msekatchev/IWCDCameraHousing/solidworks parts and assembly/PVC Parts/8in PVC Flange Closed - Dome Hole.SLDPRT

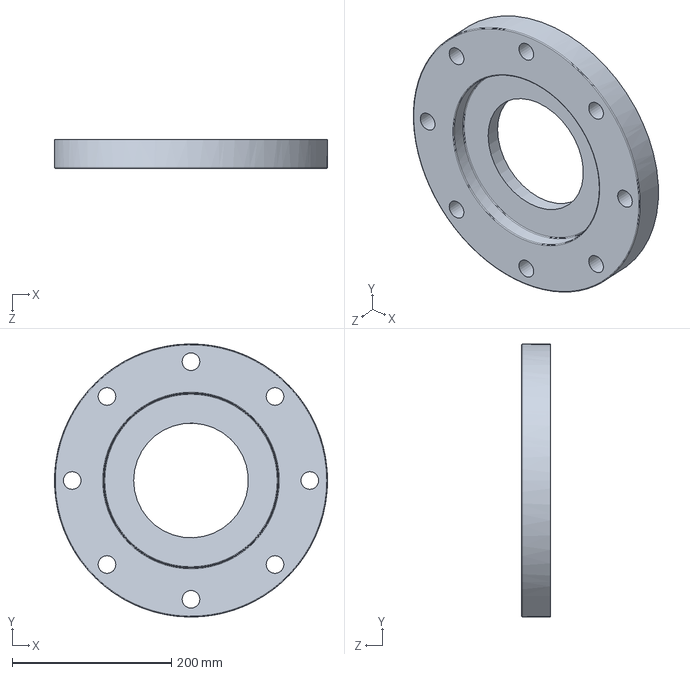
[picture p16: CAD file, 2021-06-16]
solidworks parts and assembly/PVC Parts/8in PVC Flange Closed - Dome Hole.SLDPRT
342.9 x 342.8 x 36.5 mm
