msekatchev/IWCDCameraHousing/solidworks parts and assembly/piston-FrontRing.SLDPRT

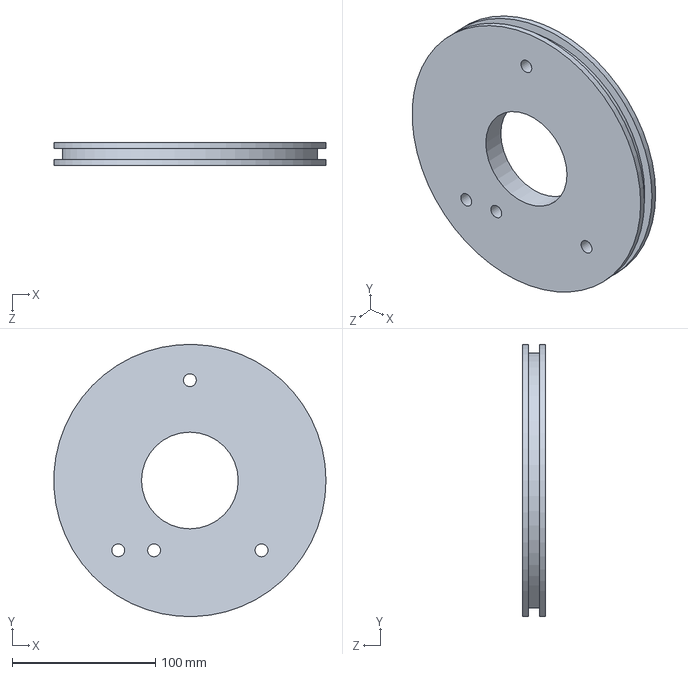
[picture p17: CAD file, 2021-06-16]
solidworks parts and assembly/piston-FrontRing.SLDPRT
189.8 x 189.9 x 16.0 mm
