msekatchev/IWCDCameraHousing/solidworks parts and assembly/PVC Parts/8in PVC Cap.SLDPRT

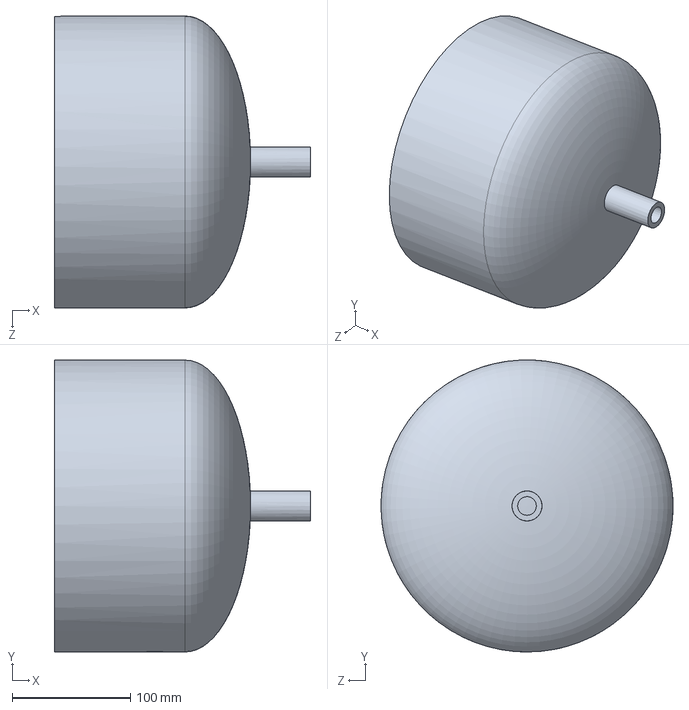
[picture p18: CAD file, 2021-04-09]
solidworks parts and assembly/PVC Parts/8in PVC Cap.SLDPRT
216.9 x 247.1 x 247.1 mm
