msekatchev/IWCDCameraHousing/metalHousingDesign/6 INCH Rayotek Dome.SLDPRT

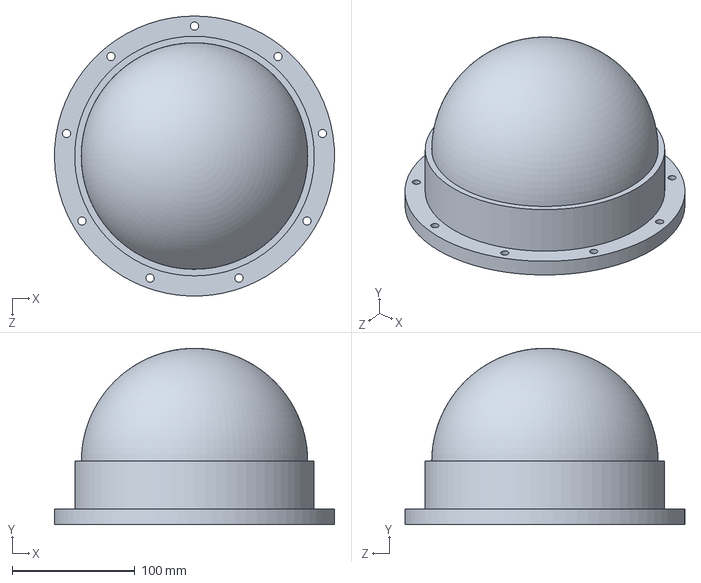
[picture p19: CAD file, 2022-03-02]
metalHousingDesign/6 INCH Rayotek Dome.SLDPRT
228.5 x 144.0 x 228.5 mm
