msekatchev/IWCDCameraHousing/solidworks parts and assembly/PVC Parts/6in PVC Pipe.SLDPRT

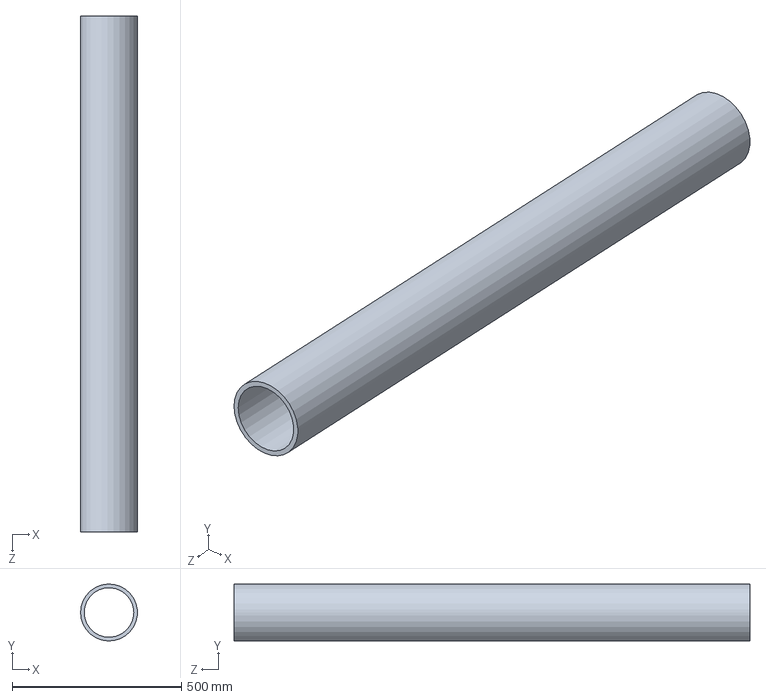
[picture p20: CAD file, 2021-04-09]
solidworks parts and assembly/PVC Parts/6in PVC Pipe.SLDPRT
168.3 x 168.0 x 1524.0 mm
