msekatchev/IWCDCameraHousing/metalHousingDesign/XDE2534-long.SLDPRT

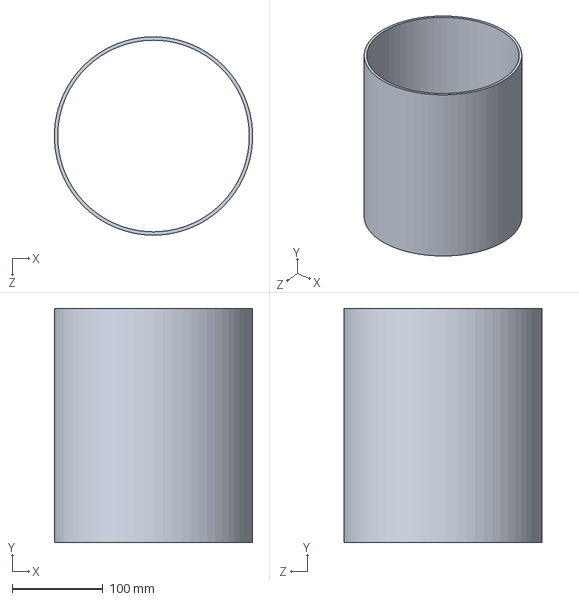
[picture p21: CAD file, 2022-01-20]
metalHousingDesign/XDE2534-long.SLDPRT
218.8 x 258.4 x 219.1 mm
