msekatchev/IWCDCameraHousing/metalHousingDesign/XDE2535.SLDPRT

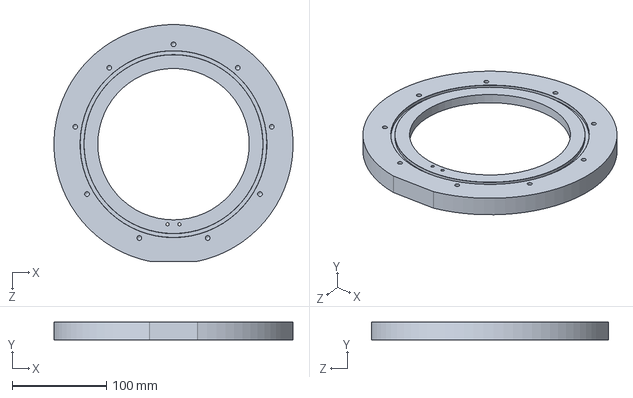
[picture p22: CAD file, 2022-01-20]
metalHousingDesign/XDE2535.SLDPRT
253.8 x 19.1 x 251.3 mm
