msekatchev/IWCDCameraHousing/solidworks parts and assembly/piston-SpacerTube.SLDPRT

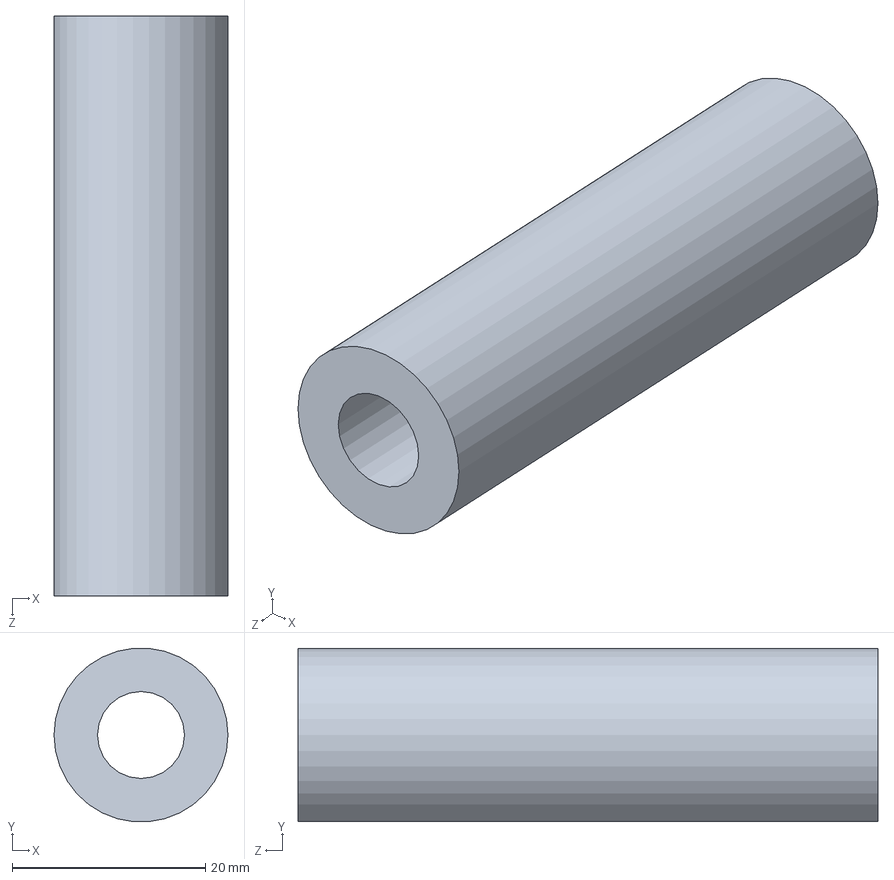
[picture p23: CAD file, 2021-04-09]
solidworks parts and assembly/piston-SpacerTube.SLDPRT
18.0 x 17.9 x 60.0 mm
