msekatchev/IWCDCameraHousing/solidworks parts and assembly/PVC Parts/8in PVC Flange Closed.SLDPRT

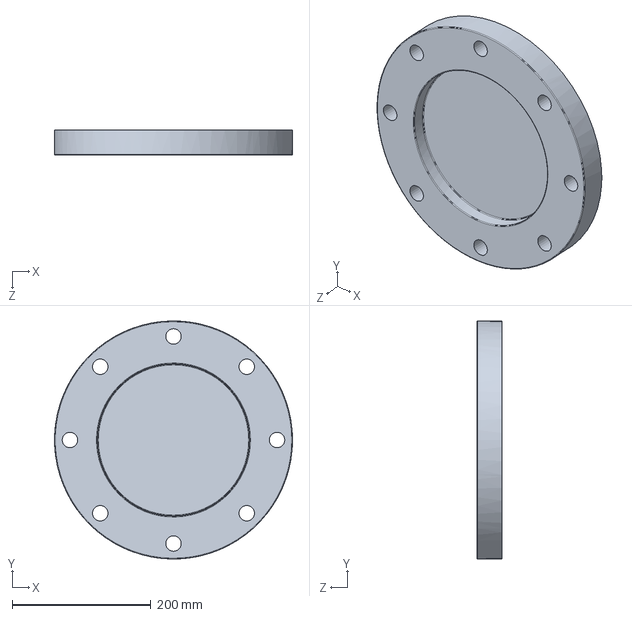
[picture p24: CAD file, 2021-04-09]
solidworks parts and assembly/PVC Parts/8in PVC Flange Closed.SLDPRT
342.9 x 342.8 x 36.5 mm
