msekatchev/IWCDCameraHousing/solidworks parts and assembly/PVC Parts/8in Buna-N Gasket.SLDPRT

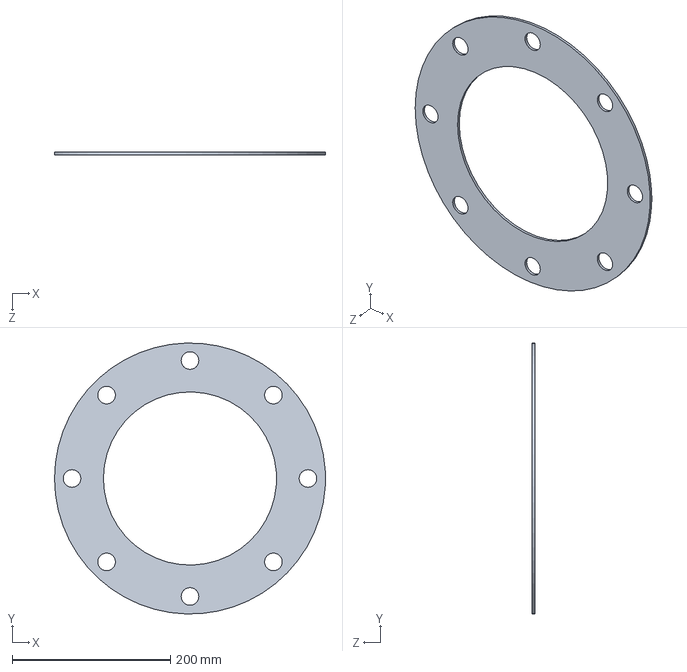
[picture p25: CAD file, 2021-04-09]
solidworks parts and assembly/PVC Parts/8in Buna-N Gasket.SLDPRT
342.9 x 342.7 x 3.17 mm
