msekatchev/IWCDCameraHousing/metalHousingDesign/XDE2540.SLDPRT

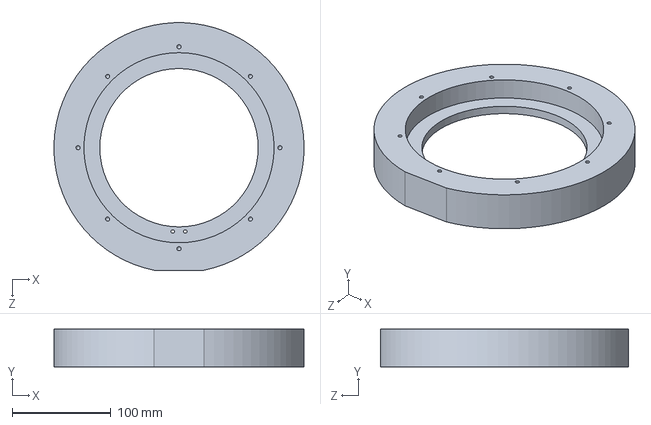
[picture p26: CAD file, 2022-01-20]
metalHousingDesign/XDE2540.SLDPRT
253.8 x 38.1 x 251.3 mm
