msekatchev/IWCDCameraHousing/solidworks parts and assembly/PVC Parts/8in PVC Pipe.SLDPRT

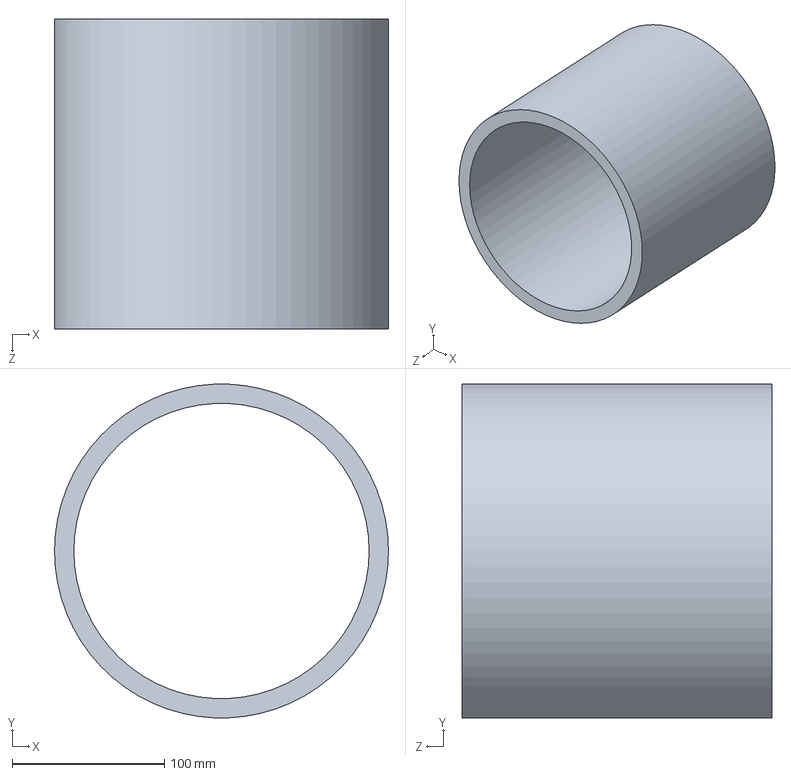
[picture p27: CAD file, 2021-04-09]
solidworks parts and assembly/PVC Parts/8in PVC Pipe.SLDPRT
219.1 x 218.8 x 203.2 mm
