msekatchev/IWCDCameraHousing/solidworks parts and assembly/SPRING.SLDPRT

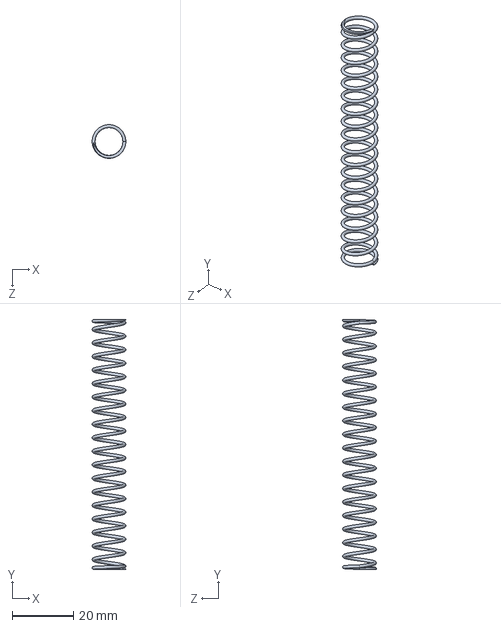
[picture p28: CAD file, 2021-04-09]
solidworks parts and assembly/SPRING.SLDPRT
11.0 x 81.5 x 11.0 mm
