msekatchev/IWCDCameraHousing/metalHousingDesign/XDE2539.SLDPRT

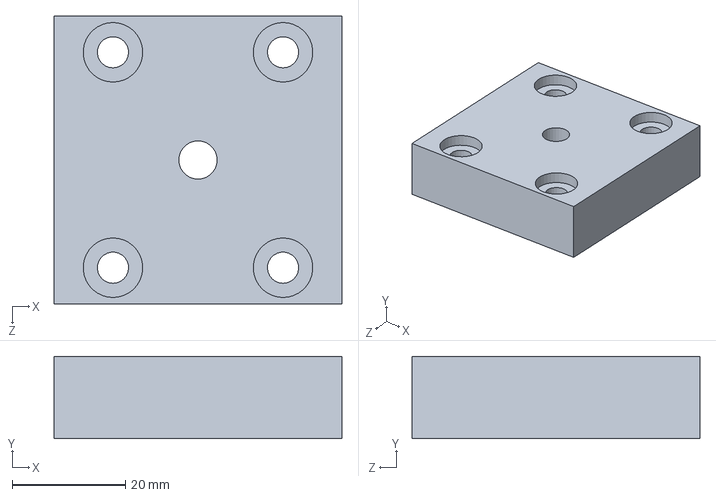
[picture p29: CAD file, 2022-01-20]
metalHousingDesign/XDE2539.SLDPRT
50.8 x 14.5 x 50.8 mm
