msekatchev/IWCDCameraHousing/solidworks parts and assembly/PVC Parts/8in PVC Flange.SLDPRT

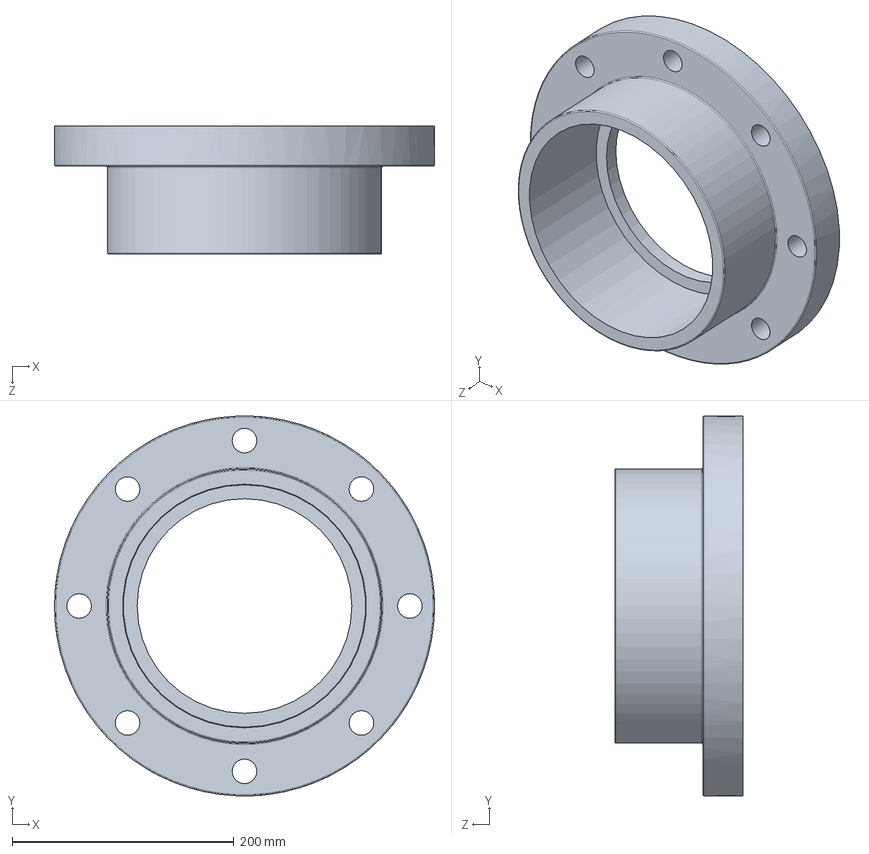
[picture p30: CAD file, 2021-04-09]
solidworks parts and assembly/PVC Parts/8in PVC Flange.SLDPRT
342.9 x 342.7 x 115.9 mm
