msekatchev/IWCDCameraHousing/metalHousingDesign/XDE2536.SLDPRT

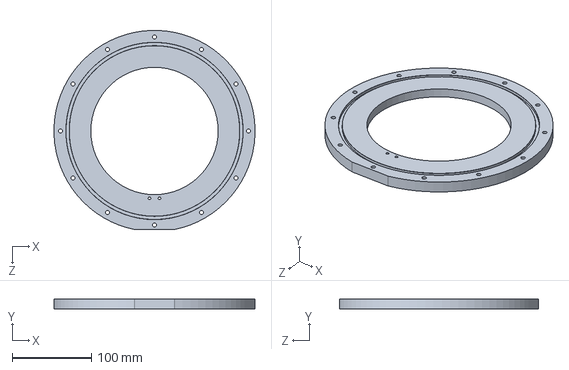
[picture p31: CAD file, 2022-01-20]
metalHousingDesign/XDE2536.SLDPRT
253.8 x 12.7 x 251.3 mm
