msekatchev/IWCDCameraHousing/metalHousingDesign/XDE2534-cut.SLDPRT

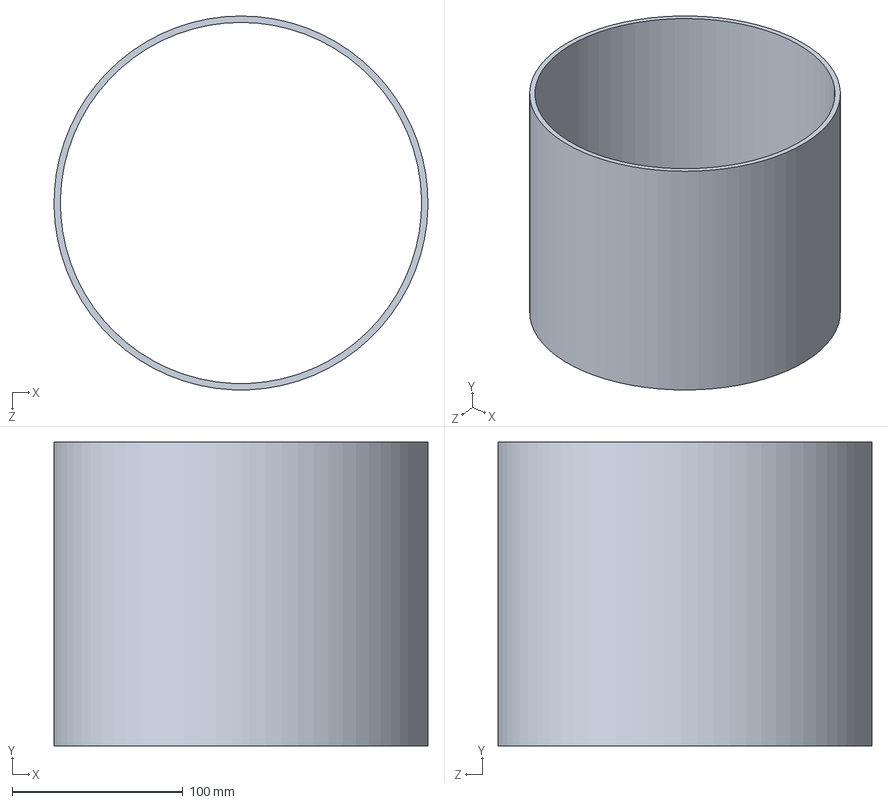
[picture p32: CAD file, 2022-01-20]
metalHousingDesign/XDE2534-cut.SLDPRT
219.0 x 178.0 x 219.1 mm
