msekatchev/IWCDCameraHousing/solidworks parts and assembly/M8 STEEL ROD.SLDPRT

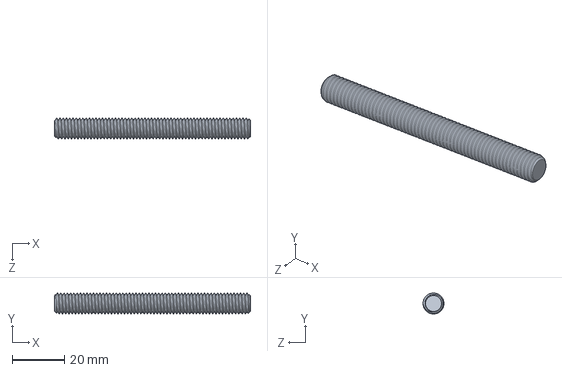
[picture p33: CAD file, 2021-04-09]
solidworks parts and assembly/M8 STEEL ROD.SLDPRT
75.0 x 8.00 x 8.00 mm
