msekatchev/IWCDCameraHousing/metalHousingDesign/XDE2557.SLDPRT

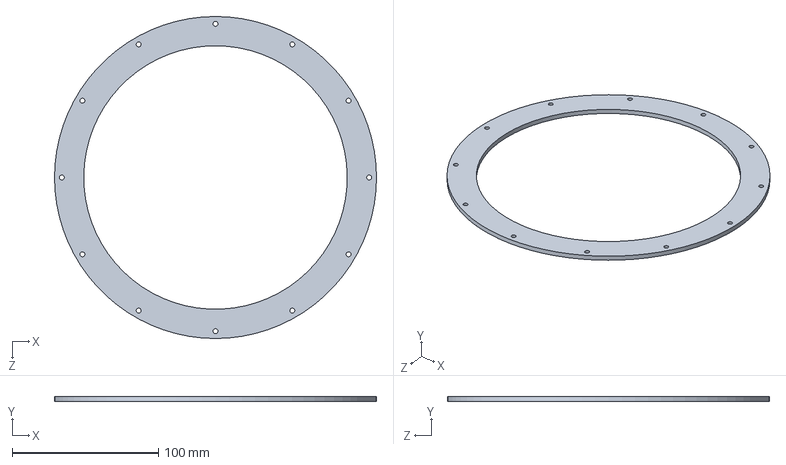
[picture p34: CAD file, 2022-01-20]
metalHousingDesign/XDE2557.SLDPRT
220.0 x 3.17 x 220.0 mm
