msekatchev/IWCDCameraHousing/metalHousingDesign/XDE2538.SLDPRT

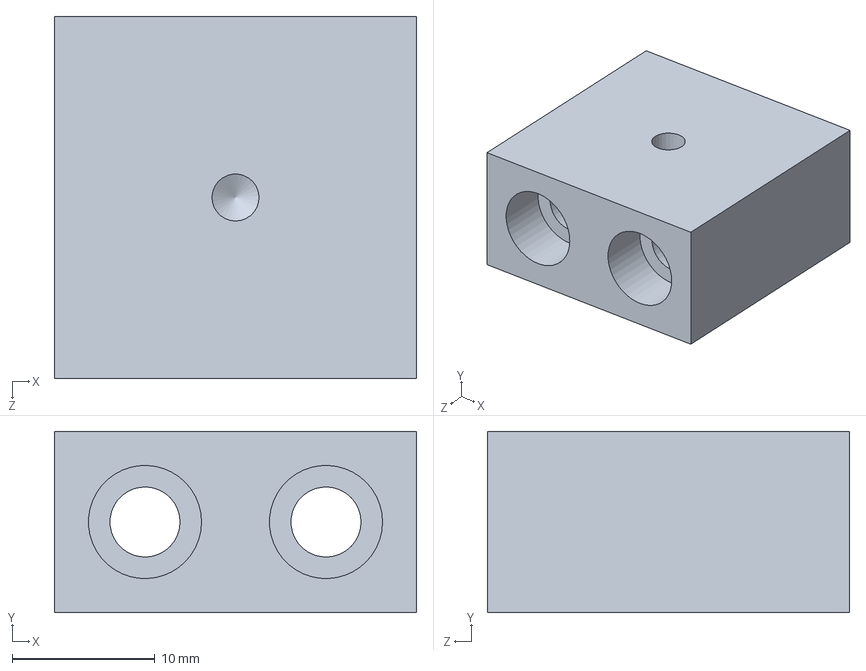
[picture p35: CAD file, 2022-01-20]
metalHousingDesign/XDE2538.SLDPRT
25.4 x 12.7 x 25.4 mm
