msekatchev/IWCDCameraHousing/solidworks parts and assembly/piston-7inO-RING.SLDPRT

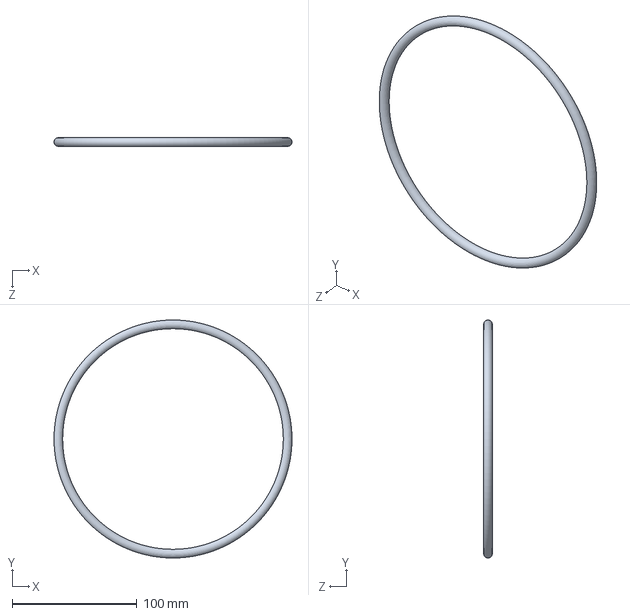
[picture p36: CAD file, 2021-04-09]
solidworks parts and assembly/piston-7inO-RING.SLDPRT
191.1 x 191.1 x 6.98 mm
