msekatchev/IWCDCameraHousing/metalHousingDesign/XDE2532_Nautilus.SLDPRT

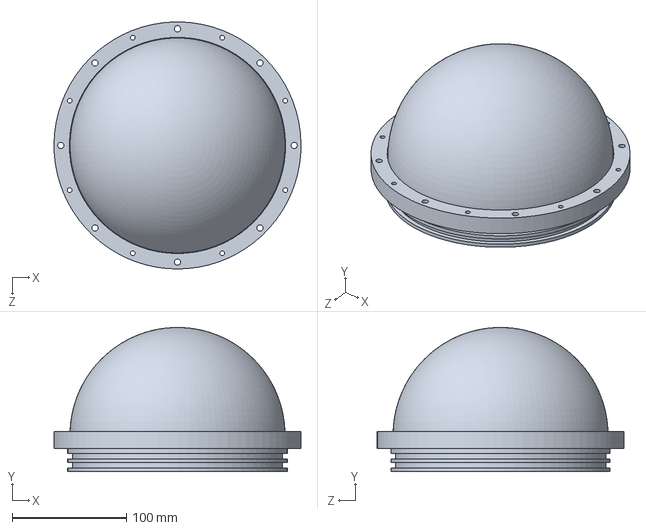
[picture p37: CAD file, 2022-01-20]
metalHousingDesign/XDE2532_Nautilus.SLDPRT
216.0 x 126.0 x 215.9 mm
