msekatchev/IWCDCameraHousing/solidworks parts and assembly/piston-CameraPlate.SLDPRT

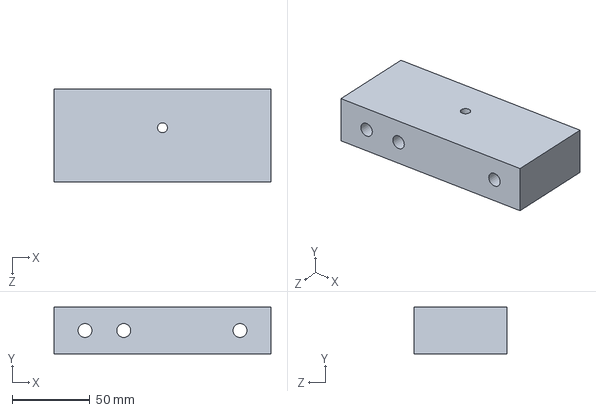
[picture p38: CAD file, 2021-04-09]
solidworks parts and assembly/piston-CameraPlate.SLDPRT
140.0 x 30.0 x 60.0 mm
