msekatchev/IWCDCameraHousing/metalHousingDesign/XDE2556.SLDPRT

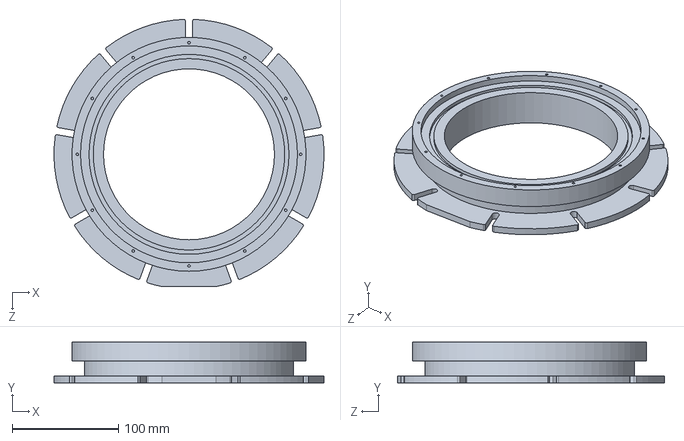
[picture p39: CAD file, 2022-01-20]
metalHousingDesign/XDE2556.SLDPRT
254.0 x 38.1 x 251.3 mm
