msekatchev/IWCDCameraHousing/metalHousingDesign/XDE2532_EZTop.SLDPRT

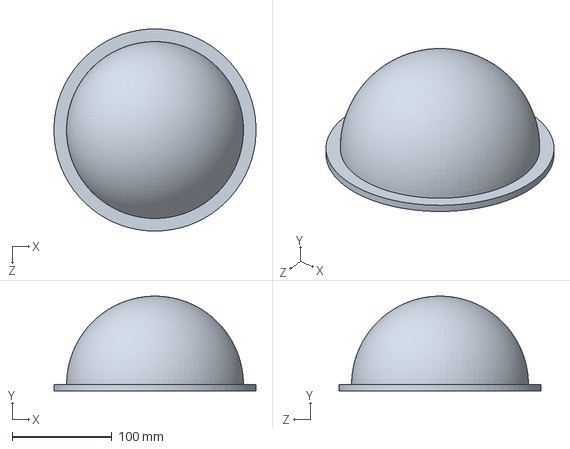
[picture p40: CAD file, 2022-01-20]
metalHousingDesign/XDE2532_EZTop.SLDPRT
203.0 x 95.2 x 203.2 mm
