msekatchev/IWCDCameraHousing/metalHousingDesign/XDE2555.SLDPRT

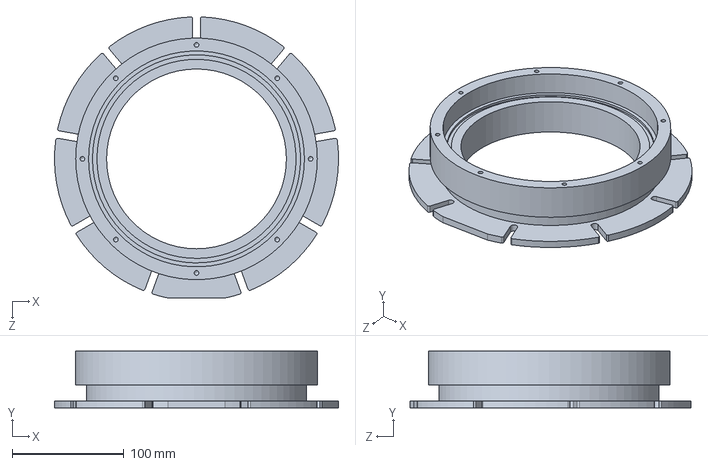
[picture p41: CAD file, 2022-01-20]
metalHousingDesign/XDE2555.SLDPRT
254.0 x 50.8 x 251.3 mm
