msekatchev/IWCDCameraHousing/solidworks parts and assembly/Camera Case-2_V2.SLDPRT

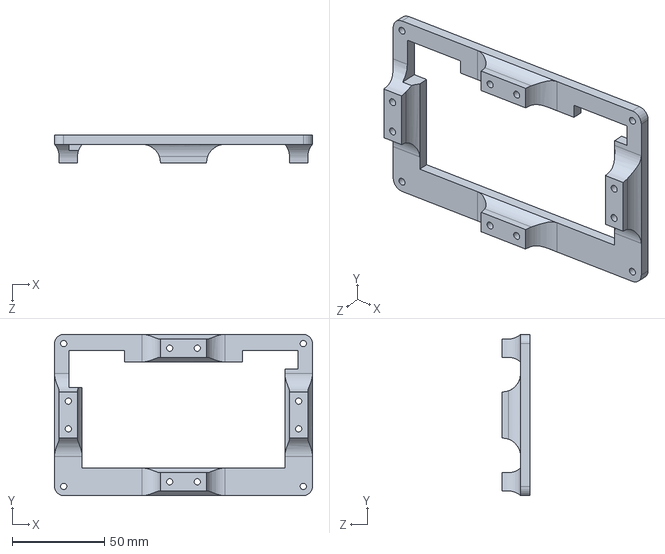
[picture p42: CAD file, 2021-02-12]
solidworks parts and assembly/Camera Case-2_V2.SLDPRT
140.0 x 87.5 x 15.0 mm
