msekatchev/IWCDCameraHousing/solidworks parts and assembly/Lightduty_Blended_EPDM_Foam_Strip_8694K124__V2.SLDPRT

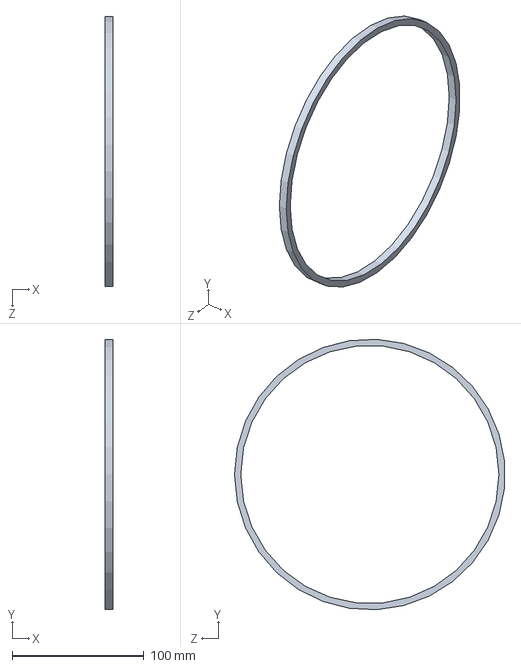
[picture p43: CAD file, 2021-02-12]
solidworks parts and assembly/Lightduty_Blended_EPDM_Foam_Strip_8694K124__V2.SLDPRT
6.35 x 205.3 x 205.0 mm
