msekatchev/IWCDCameraHousing/solidworks parts and assembly/Camera.SLDPRT

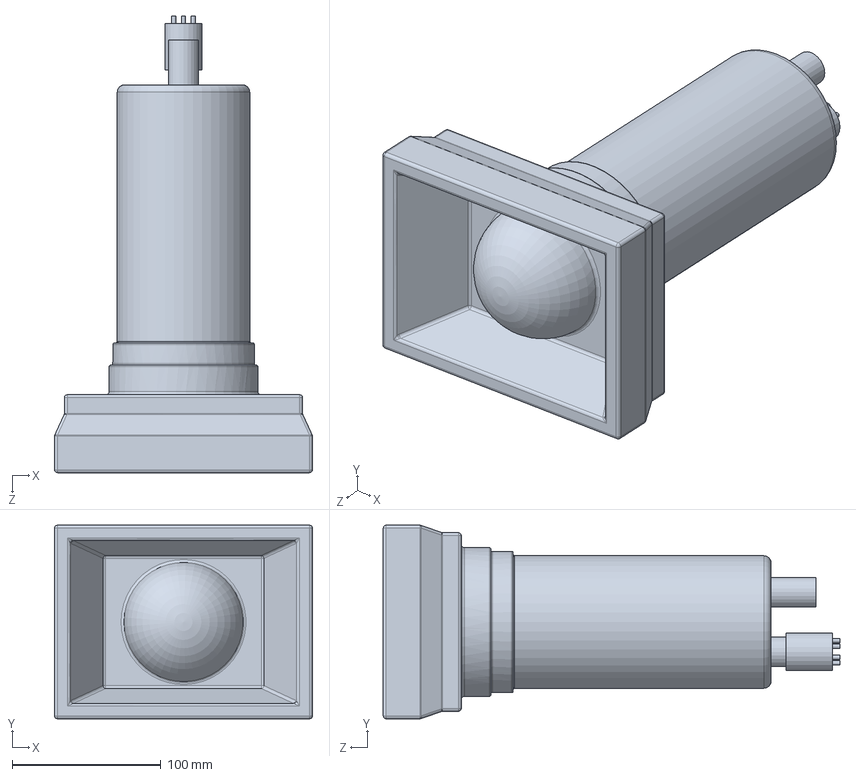
[picture p44: CAD file, 2021-02-12]
solidworks parts and assembly/Camera.SLDPRT
173.2 x 130.0 x 306.4 mm
