msekatchev/IWCDCameraHousing/solidworks parts and assembly/Camera Case.SLDPRT

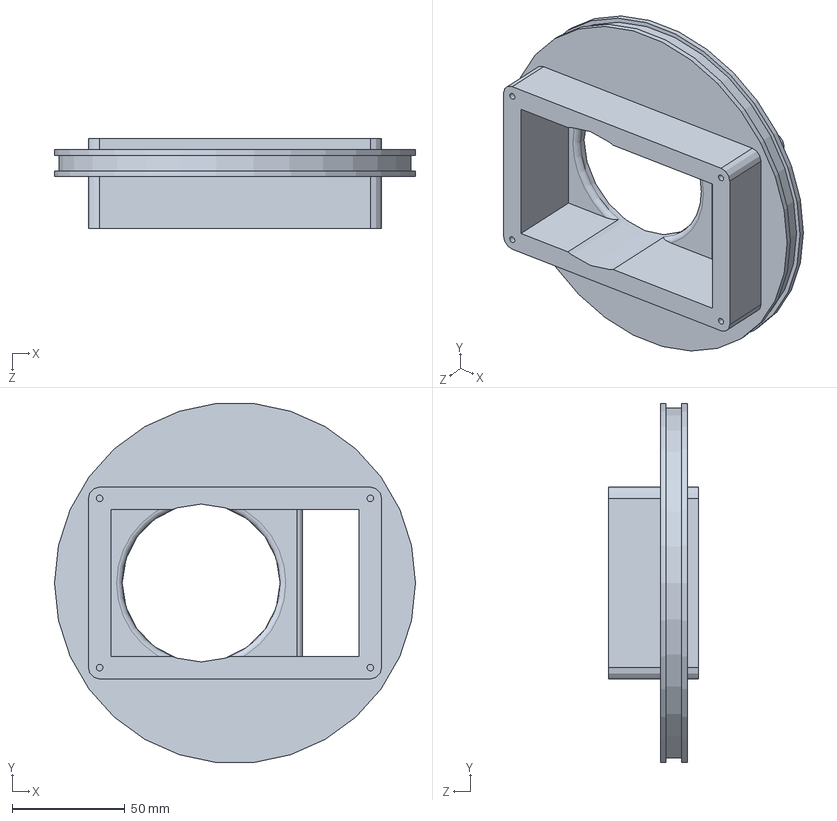
[picture p45: CAD file, 2021-02-12]
solidworks parts and assembly/Camera Case.SLDPRT
160.0 x 159.1 x 40.0 mm
