msekatchev/IWCDCameraHousing/solidworks parts and assembly/O-ring 210mm.SLDPRT

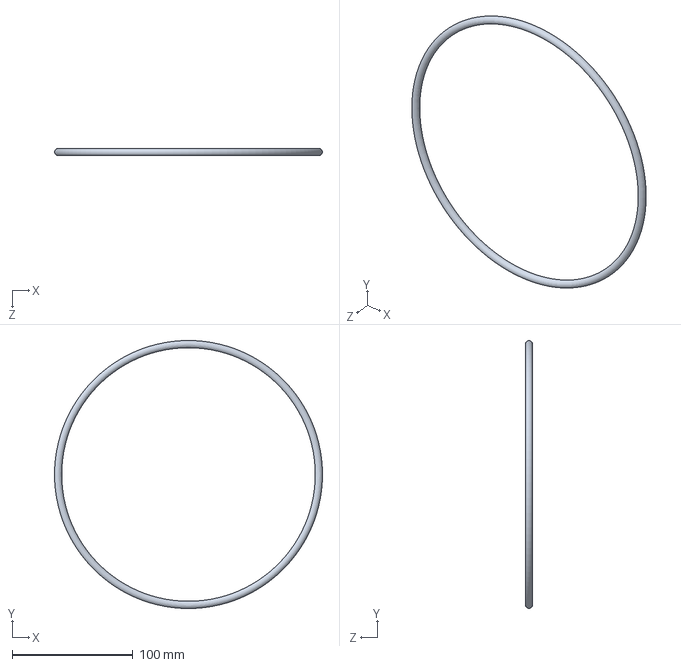
[picture p46: CAD file, 2021-02-12]
solidworks parts and assembly/O-ring 210mm.SLDPRT
222.0 x 222.0 x 6.00 mm
