msekatchev/IWCDCameraHousing/solidworks parts and assembly/Lens.SLDPRT

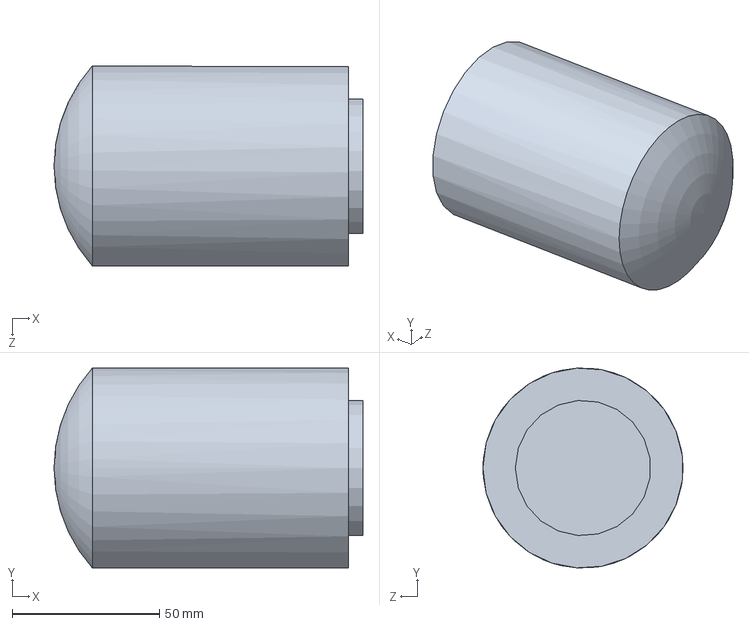
[picture p47: CAD file, 2021-02-12]
solidworks parts and assembly/Lens.SLDPRT
105.0 x 67.9 x 68.0 mm
