msekatchev/IWCDCameraHousing/solidworks parts and assembly/Back Plate_V2.SLDPRT

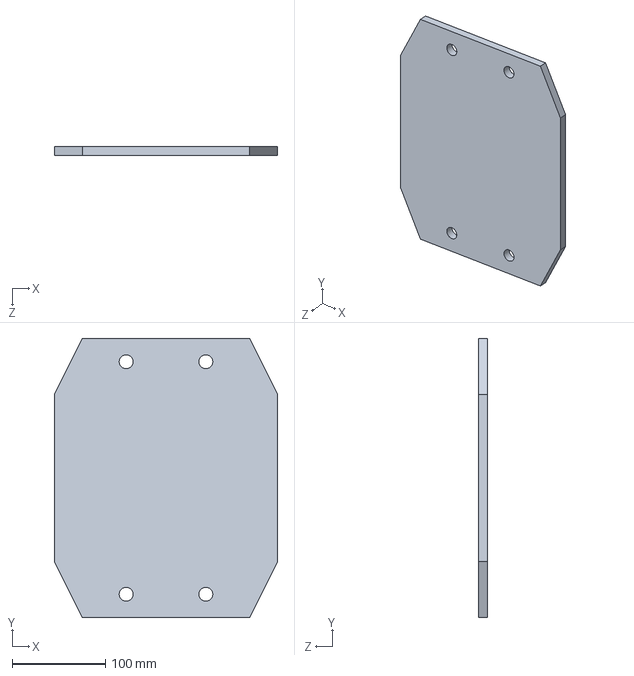
[picture p48: CAD file, 2021-02-12]
solidworks parts and assembly/Back Plate_V2.SLDPRT
240.0 x 300.0 x 10.0 mm
