msekatchev/IWCDCameraHousing/solidworks parts and assembly/Pillars.SLDPRT

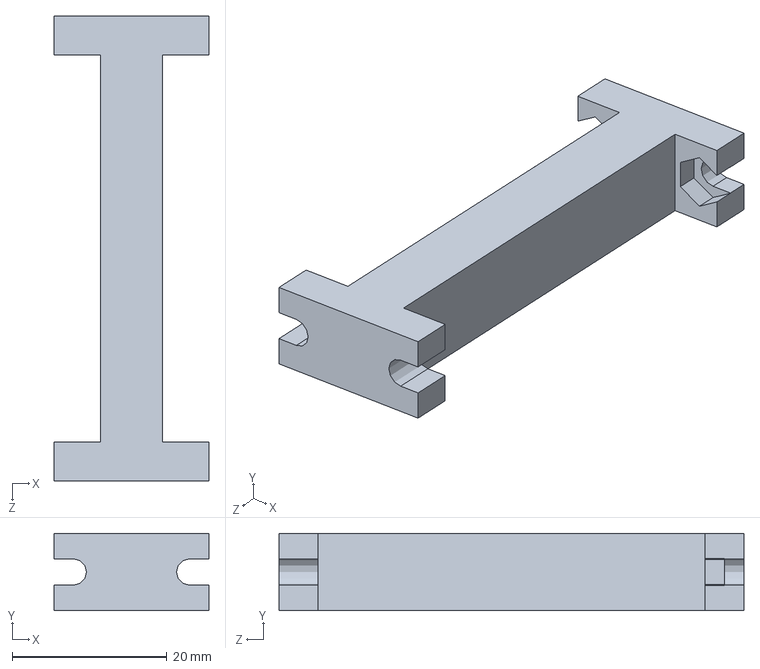
[picture p49: CAD file, 2021-02-12]
solidworks parts and assembly/Pillars.SLDPRT
20.0 x 10.0 x 60.0 mm
