msekatchev/IWCDCameraHousing/solidworks parts and assembly/Custom_Cylinder_v2.SLDPRT

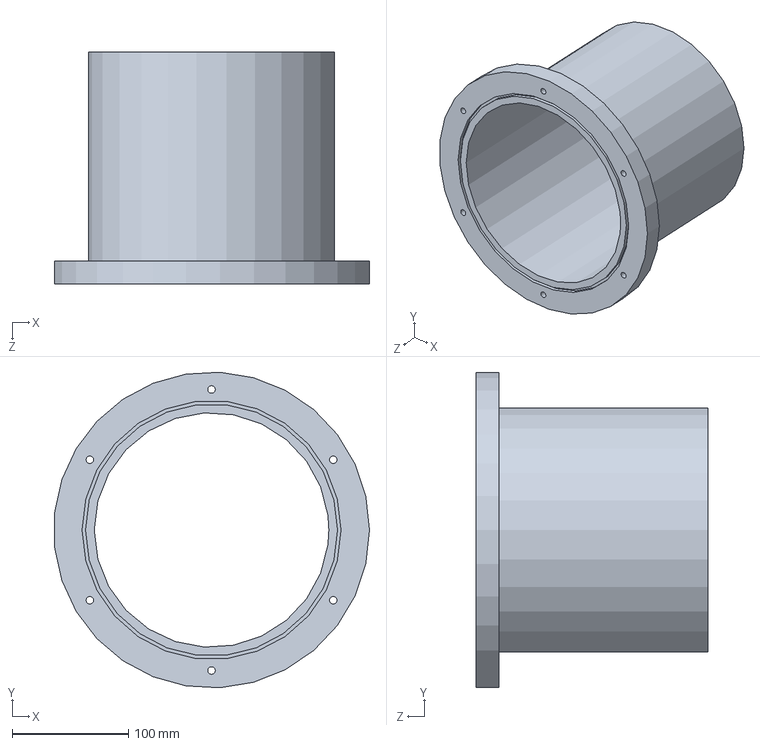
[picture p50: CAD file, 2021-02-12]
solidworks parts and assembly/Custom_Cylinder_v2.SLDPRT
271.2 x 271.6 x 200.0 mm
