msekatchev/IWCDCameraHousing/solidworks parts and assembly/camera case V3.SLDPRT

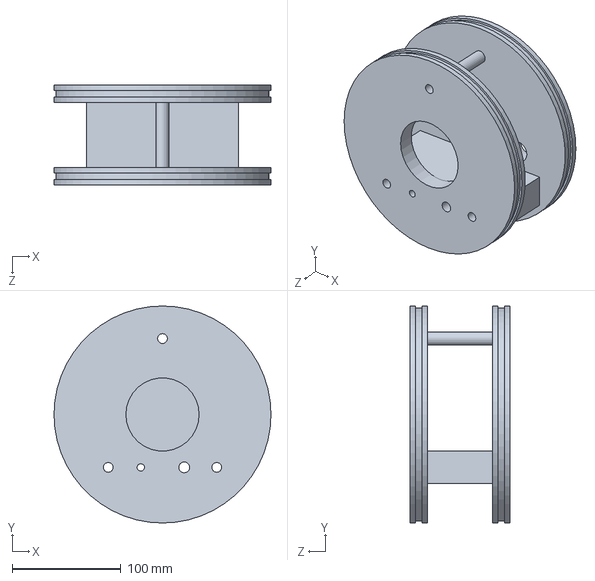
[picture p51: CAD file, 2021-02-12]
solidworks parts and assembly/camera case V3.SLDPRT
200.0 x 200.0 x 92.0 mm
